Loicandre/LED_PWM_Controller/DOC/IMG_20200929_101454.jpg

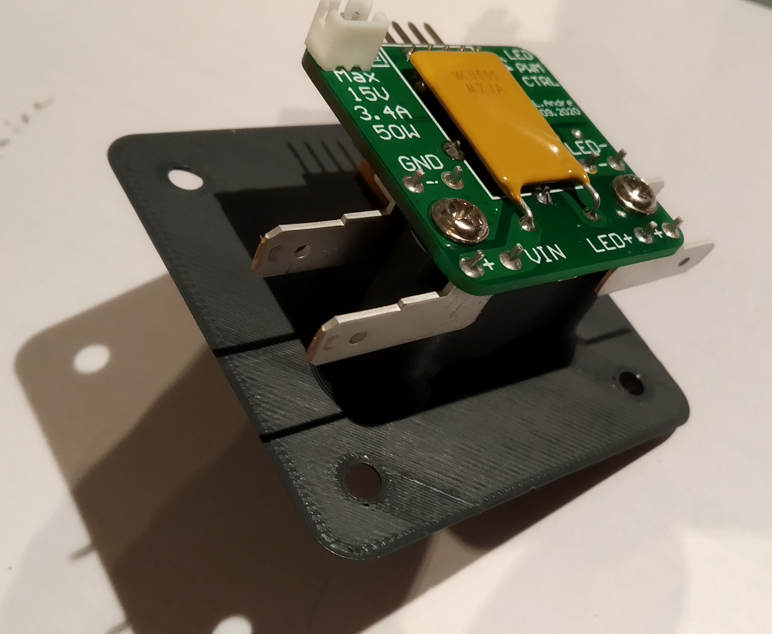
DOC/IMG_20200929_101454.jpg
